LiangXiaohan506/Plantar-pressure-system-V2.0/Software/Core/Src/i2c.c

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
/* Includes ------------------------------------------------------------------*/
#include "i2c.h"

I2C_HandleTypeDef hi2c2;

/* I2C2 init function */
void MX_I2C2_Init(void)
{

  hi2c2.Instance = I2C2;
  hi2c2.Init.ClockSpeed = 400000;
  hi2c2.Init.DutyCycle = I2C_DUTYCYCLE_2;
  hi2c2.Init.OwnAddress1 = 0;
  hi2c2.Init.AddressingMode = I2C_ADDRESSINGMODE_7BIT;
  hi2c2.Init.DualAddressMode = I2C_DUALADDRESS_DISABLE;
  hi2c2.Init.OwnAddress2 = 0;
  hi2c2.Init.GeneralCallMode = I2C_GENERALCALL_DISABLE;
  hi2c2.Init.NoStretchMode = I2C_NOSTRETCH_DISABLE;
  if (HAL_I2C_Init(&hi2c2) != HAL_OK)
  {
    Error_Handler();
  }
}

void HAL_I2C_MspInit(I2C_HandleTypeDef* i2cHandle)
{

  GPIO_InitTypeDef GPIO_InitStruct = {0};
  if(i2cHandle->Instance==I2C2)
  {
    __HAL_RCC_GPIOB_CLK_ENABLE();
    /**I2C2 GPIO Configuration
    PB10     ------> I2C2_SCL
    PB11     ------> I2C2_SDA
    */
    GPIO_InitStruct.Pin = GPIO_PIN_10|GPIO_PIN_11;
    GPIO_InitStruct.Mode = GPIO_MODE_AF_OD;
    GPIO_InitStruct.Speed = GPIO_SPEED_FREQ_HIGH;
    HAL_GPIO_Init(GPIOB, &GPIO_InitStruct);

    /* I2C2 clock enable */
    __HAL_RCC_I2C2_CLK_ENABLE();
  }
}

void HAL_I2C_MspDeInit(I2C_HandleTypeDef* i2cHandle)
{

  if(i2cHandle->Instance==I2C2)
  {
    /* Peripheral clock disable */
    __HAL_RCC_I2C2_CLK_DISABLE();

    /**I2C2 GPIO Configuration
    PB10     ------> I2C2_SCL
    PB11     ------> I2C2_SDA
    */
    HAL_GPIO_DeInit(GPIOB, GPIO_PIN_10);

    HAL_GPIO_DeInit(GPIOB, GPIO_PIN_11);

  }
}

/* USER CODE BEGIN 1 */
////IIC写寄存器数据
//int i2cWrite(uint8_t addr, uint8_t reg, uint8_t len, uint8_t *data)
//{
//	HAL_I2C_Mem_Write(&hi2c2,addr,reg,I2C_MEMADD_SIZE_8BIT,data,len,0xfff);
//	return 0;
//}

////IIC读寄存器数据
//int i2cRead(uint8_t addr, uint8_t reg, uint8_t len, uint8_t *buf)
//{
//	HAL_I2C_Mem_Read(&hi2c2,addr,reg,I2C_MEMADD_SIZE_8BIT,buf,len,0xfff);
//	return 0;
//}

///**************************实现函数********************************************
//*函数原型:		unsigned char I2C_ReadOneByte(unsigned char I2C_Addr,unsigned char addr)
//*功　　能:	  读取指定设备 指定寄存器的一个值
//*输    入:	I2C_Addr  目标设备地址
//		        addr	    寄存器地址
//*返    回:  读出来的值
//*******************************************************************************/ 
//unsigned char I2C_ReadOneByte(unsigned char I2C_Addr, unsigned char addr)
//{
//	unsigned char buf=0;
//	HAL_I2C_Mem_Read(&hi2c2,I2C_Addr,addr,I2C_MEMADD_SIZE_8BIT,&buf,1,0xff);
//	return buf;
//}

///**************************实现函数********************************************
//*函数原型:		u8 IICreadBytes(u8 dev, u8 reg, u8 length, u8 *data)
//*功　　能:	  读取指定设备 指定寄存器的 length个值
//*输    入:	dev     目标设备地址
//		        reg	    寄存器地址
//		        length  要读的字节数
//		        data    读出的数据将要存放的指针
//*返    回:  读出来的字节数量
//*******************************************************************************/ 
//uint8_t IICreadBytes(uint8_t dev, uint8_t reg, uint8_t length, uint8_t *data)
//{
//	HAL_I2C_Mem_Read(&hi2c2,dev,reg,I2C_MEMADD_SIZE_8BIT,data,length,0xff);
//  return 1;
//}

///**************************实现函数********************************************
//*函数原型:		u8 IICwriteBytes(u8 dev, u8 reg, u8 length, u8* data)
//*功　　能:	  将多个字节写入指定设备 指定寄存器
//*输    入:	dev     目标设备地址
//		        reg	    寄存器地址
//		        length  要写的字节数
//		        data    将要写的数据的首地址
//*返    回:  返回是否成功
//*******************************************************************************/ 
//uint8_t IICwriteBytes(uint8_t dev, uint8_t reg, uint8_t length, uint8_t* data)
//{
//	if(HAL_I2C_Mem_Write(&hi2c2,dev,reg,I2C_MEMADD_SIZE_8BIT,data,length,0xff) == HAL_OK)
//		return 1;
//	else
//		return 0;
//}

///**************************实现函数********************************************
//*函数原型:		u8 IICreadByte(u8 dev, u8 reg, u8 *data)
//*功　　能:	  读取指定设备 指定寄存器的一个值
//*输    入:	dev    目标设备地址
//		        reg	   寄存器地址
//		        data   读出的数据将要存放的地址
//*返    回:  1
//*******************************************************************************/ 
//uint8_t IICreadByte(uint8_t dev, uint8_t reg, uint8_t *data)
//{
//	*data=I2C_ReadOneByte(dev, reg);
//  return 1;
//}


///**************************实现函数********************************************
//*函数原型:		unsigned char IICwriteByte(unsigned char dev, unsigned char reg, unsigned char data)
//*功　　能:	  写入指定设备 指定寄存器一个字节
//*输    入:	dev    目标设备地址
//		        reg	   寄存器地址
//		        data   将要写入的字节
//*返    回:  1
//*******************************************************************************/ 
//unsigned char IICwriteByte(unsigned char dev, unsigned char reg, unsigned char data)
//{
//    return IICwriteBytes(dev, reg, 1, &data);
//}

///**************************实现函数********************************************
//*函数原型:		u8 IICwriteBits(u8 dev,u8 reg,u8 bitStart,u8 length,u8 data)
//*功　　能:	  读 修改 写 指定设备 指定寄存器一个字节 中的多个位
//*输    入:	dev       目标设备地址
//		        reg	      寄存器地址
//		        bitStart  目标字节的起始位
//		        length    位长度
//		        data      存放改变目标字节位的值
//*返    回:  成功 为1 
// 		        失败为0
//*******************************************************************************/ 
//uint8_t IICwriteBits(uint8_t dev,uint8_t reg,uint8_t bitStart,uint8_t length,uint8_t data)
//{

//    uint8_t b;
//    if(IICreadByte(dev, reg, &b) != 0) 
//		{
//        uint8_t mask = (0xFF << (bitStart + 1)) | 0xFF >> ((8 - bitStart) + length - 1);
//        data <<= (8 - length);
//        data >>= (7 - bitStart);
//        b &= mask;
//        b |= data;
//        return IICwriteByte(dev, reg, b);
//    } 
//		else 
//		{
//        return 0;
//    }
//}

///**************************实现函数********************************************
//*函数原型:		u8 IICwriteBit(u8 dev, u8 reg, u8 bitNum, u8 data)
//*功　　能:	  读 修改 写 指定设备 指定寄存器一个字节 中的1个位
//*输    入:	dev     目标设备地址
//		        reg	    寄存器地址
//		        bitNum  要修改目标字节的bitNum位
//		        data    为0 时，目标位将被清0 否则将被置位
//*返    回:  成功 为1 
// 		        失败 为0
//*******************************************************************************/ 
//uint8_t IICwriteBit(uint8_t dev, uint8_t reg, uint8_t bitNum, uint8_t data){
//    uint8_t b;
//    IICreadByte(dev, reg, &b);
//    b = (data != 0) ? (b | (1 << bitNum)) : (b & ~(1 << bitNum));
//    return IICwriteByte(dev, reg, b);
//}
/* USER CODE END 1 */
